kaiquesotti/Fotometro_ESP32_Supermini/Fotos fotômetro/IMG_20260525_142237.jpg

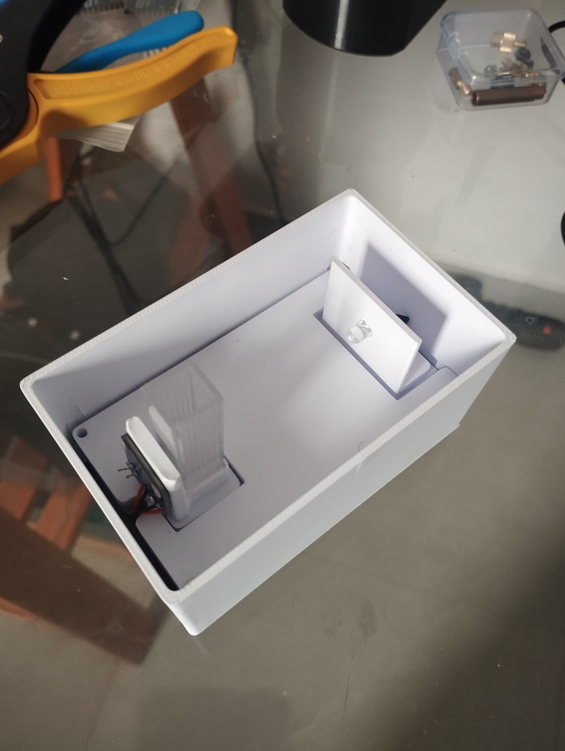
Fotos fotômetro/IMG_20260525_142237.jpg
