kaiquesotti/Fotometro_ESP32_Supermini/Fotos fotômetro/IMG_20260525_142244.jpg

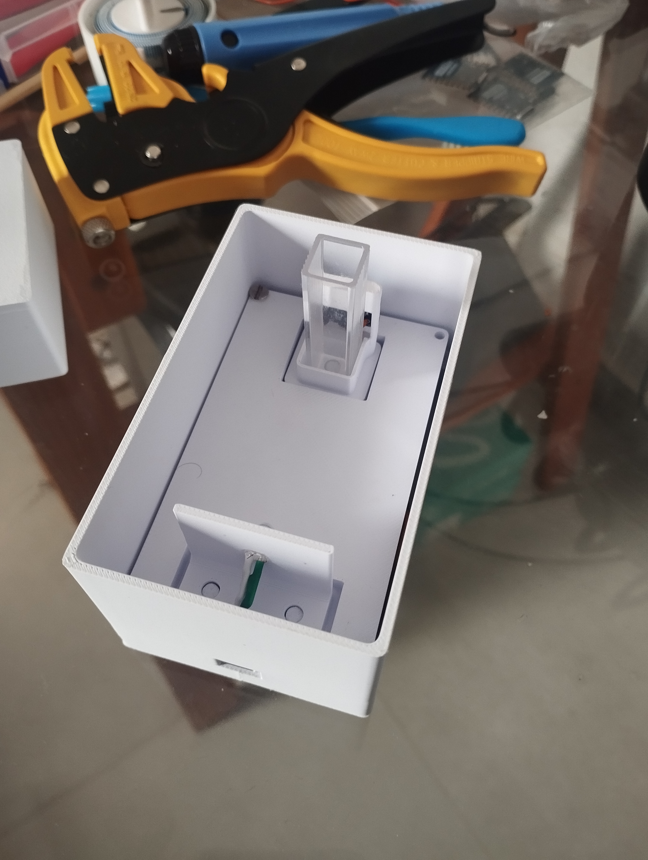
Fotos fotômetro/IMG_20260525_142244.jpg
